nooneknowspeter/orbtronics-l1-mechatronics-engineer/cad/assets/models/grabcad/am2302-dht22-temperature-and-humidity-sensor-1.snapshot.1/AM2302_001.png

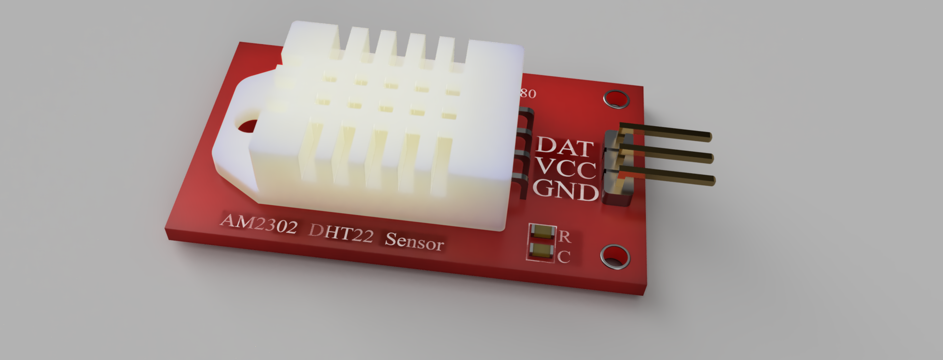
cad/assets/models/grabcad/am2302-dht22-temperature-and-humidity-sensor-1.snapshot.1/AM2302_001.png
