nooneknowspeter/orbtronics-l1-mechatronics-engineer/cad/assets/models/grabcad/b2b-jst-xh-90-degree-connector-generic-1.snapshot.3/CONECTOR-2/4.1.png

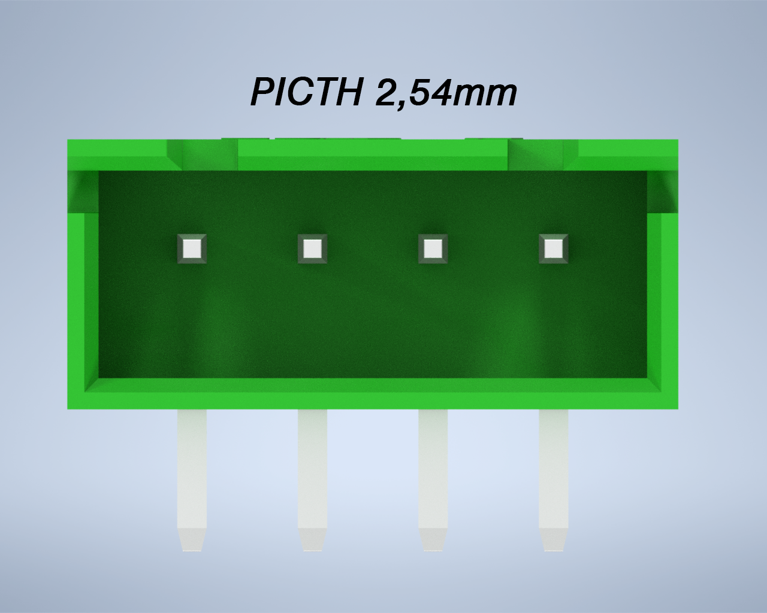
cad/assets/models/grabcad/b2b-jst-xh-90-degree-connector-generic-1.snapshot.3/CONECTOR-2/4.1.png
