nooneknowspeter/orbtronics-l1-mechatronics-engineer/cad/assets/models/grabcad/dht-22-1.snapshot.2/DHT22.JPG

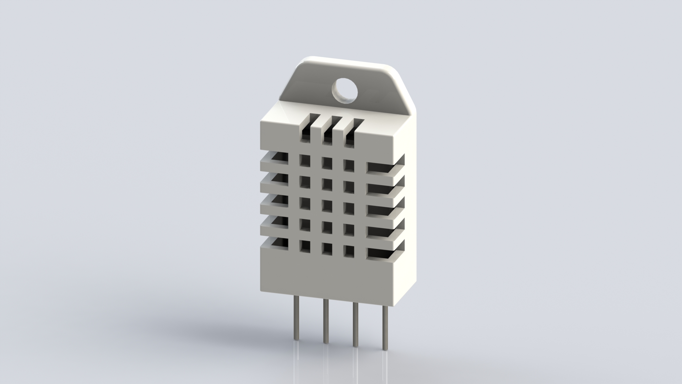
cad/assets/models/grabcad/dht-22-1.snapshot.2/DHT22.JPG
