nooneknowspeter/orbtronics-l1-mechatronics-engineer/cad/assets/models/grabcad/micro-usb-plug-2.snapshot.6/Extras_MicroUSB_01_dof_w.png

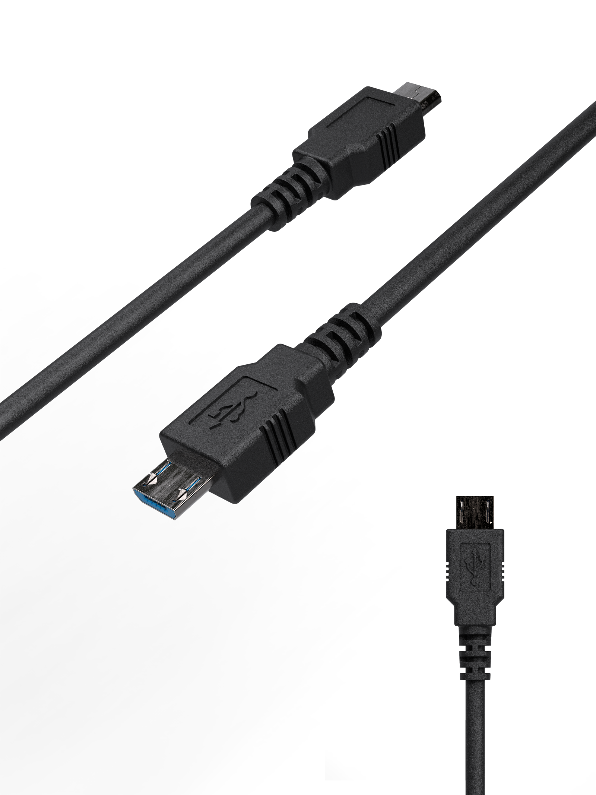
cad/assets/models/grabcad/micro-usb-plug-2.snapshot.6/Extras_MicroUSB_01_dof_w.png
