nooneknowspeter/orbtronics-l1-mechatronics-engineer/cad/assets/models/grabcad/micro-usb-plug-2.snapshot.6/Micro USB Plug.step

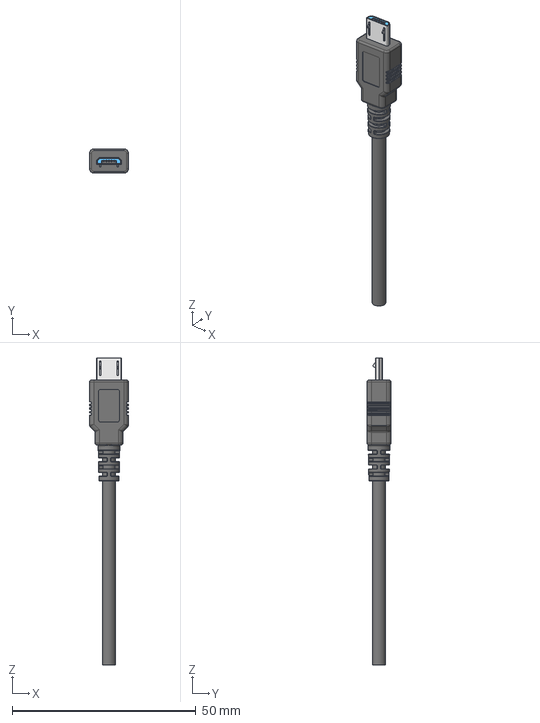
[picture p33: CAD file, 2025-08-13]
cad/assets/models/grabcad/micro-usb-plug-2.snapshot.6/Micro USB Plug.step
10.6 x 6.60 x 83.5 mm
Cable
Micro_USB_Plug_Connector
