nooneknowspeter/orbtronics-l1-mechatronics-engineer/cad/assets/models/grabcad/slide-switch-2sp-1.snapshot.1/Switch2SP.step

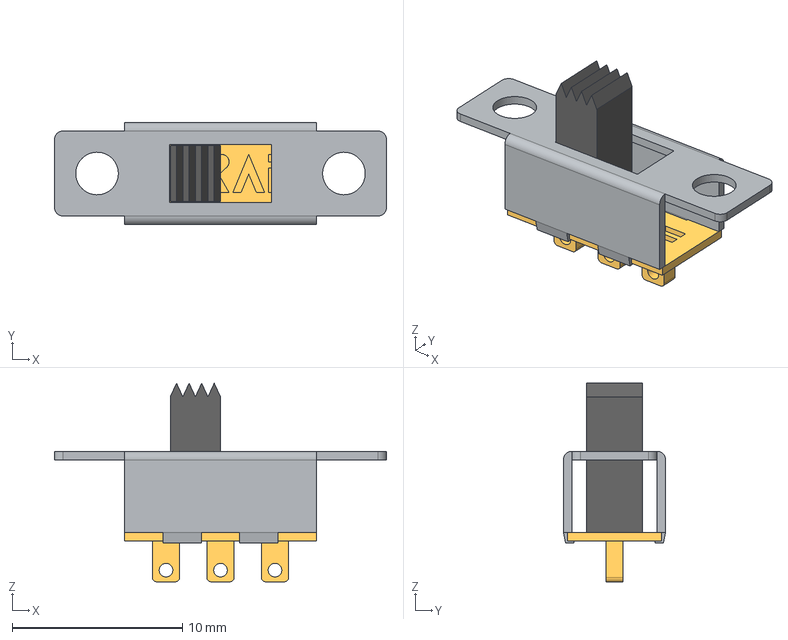
[picture p34: CAD file, 2025-08-13]
cad/assets/models/grabcad/slide-switch-2sp-1.snapshot.1/Switch2SP.step
19.5 x 6.00 x 11.7 mm
Housing
Endplate
Switch
