nooneknowspeter/orbtronics-l1-mechatronics-engineer/cad/assets/models/grabcad/b2b-jst-xh-90-degree-connector-generic-1.snapshot.3/CONECTOR-2/BLACK/BLACK JST XH 12 PIN CONNECTOR - P 2.54mm - ANGLED.stp

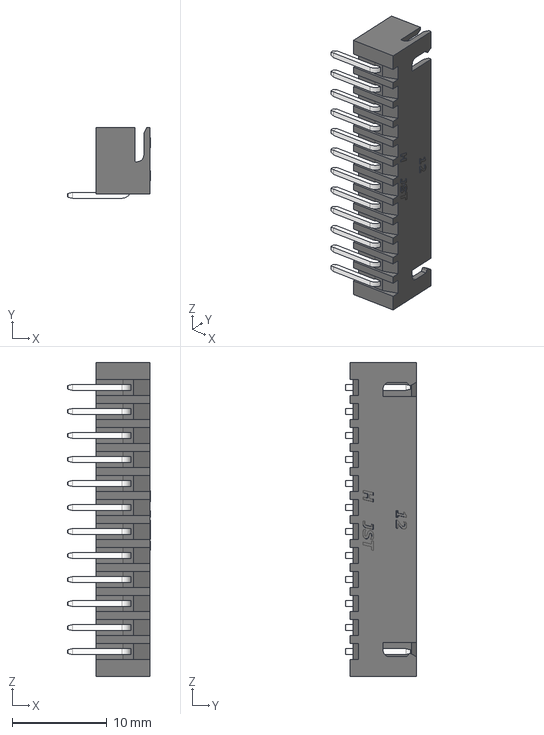
[picture p35: CAD file, 2025-08-13]
cad/assets/models/grabcad/b2b-jst-xh-90-degree-connector-generic-1.snapshot.3/CONECTOR-2/BLACK/BLACK JST XH 12 PIN CONNECTOR - P 2.54mm - ANGLED.stp
8.73 x 7.46 x 33.2 mm
